bleroy/pokeymax/VHDL/SID/jsiddevice.ini

[JSIDDevice]
; hostname to listen to clients on
Hostname=127.0.0.1
; port to listen to clients on
Port=6581
; c64 clocks, almost same as us
Latency=250000

[Audio]
; Allows overriding of the default playback/record frequency. The frequency must be provided in Hertz (Hz) and by default it is set to 44100.
Frequency=48000
; Sampling method in use
Sampling=Decimate
; Size of the audio buffer (responsiveness=1024 .. stable audio=16384), must be a power of two!
Audio Buffer Size=2048

[WhatsSID]
; WhatsSID? Recognizes the currently played tune after a few seconds
Enable=false
; The server side is in fact JSIDPlay2 running in server mode
Url=https://haendel.ddns.net:8443/jsidplay2service/JSIDPlay2REST
Username=jsidplay2
Password=jsidplay2!
; Capture the last N seconds for tune recognition
Capture Time=15
; Tune recognition will be done periodically after this time (in seconds) 
Match Retry Time=15
; Minimum relative confidence to recognize a tune with confidence
Minimum Relative Confidence=4.5

[FilterLight8580]
Filter8580CurvePosition = 13400

[FilterAverage8580]
Filter8580CurvePosition = 12500

[FilterDark8580]
Filter8580CurvePosition = 11700

[FilterLightest6581]
Filter6581CurvePosition = 0.1

[FilterLighter6581]
Filter6581CurvePosition = 0.3

[FilterLight6581]
Filter6581CurvePosition = 0.4

[FilterAverage6581]
Filter6581CurvePosition = 0.5

[FilterDark6581]
Filter6581CurvePosition = 0.6

[FilterDarker6581]
Filter6581CurvePosition = 0.7

[FilterDarkest6581]
Filter6581CurvePosition = 0.9

[FilterJSidDevice10_6581]
Attenuation=0.5
Nonlinearity=3.3e6
VoiceNonlinearity=0.96
Type3BaseResistance=1.3e6
Type3Offset=1.9e7
Type3Steepness=1.0066
Type3MinimumFETResistance=1.8e4
ResonanceFactor=1.0

[FilterJSidDevice10_8580]				
Type4K=6.55
Type4B=20
VoiceNonlinearity=1.0
ResonanceFactor=1.0

[FilterTrurl8580R5_1489]
Type4K=5.7
Type4B=20
VoiceNonlinearity=1.0
ResonanceFactor=1.0

[FilterTrurl8580R5_3691]
Type4K=6.55
Type4B=20
VoiceNonlinearity=1.0
ResonanceFactor=1.0

[FilterReSID6581]
Attenuation=0.5
Nonlinearity=3.3e6
VoiceNonlinearity=0.96
Type3BaseResistance=1537690.1305811733
Type3Offset=76322577.13241087
Type3Steepness=1.0072175060266852
Type3MinimumFETResistance=19114.018733380854
ResonanceFactor=1.0

[FilterAlankila6581R4AR_3789]
Attenuation=0.5
Nonlinearity=3.3e6
VoiceNonlinearity=0.9613160610660189
Type3BaseResistance=1147036.4394268463
Type3Offset=274228796.97550374
Type3Steepness=1.0066634233403395
Type3MinimumFETResistance=16125.154840564108
ResonanceFactor=1.0

[FilterAlankila6581R3_3984_1]
Attenuation=0.5
Nonlinearity=3.3e6
VoiceNonlinearity=0.96
Type3BaseResistance=1522171.922983084
Type3Offset=21729926.667291082
Type3Steepness=1.004994802537475
Type3MinimumFETResistance=14299.149638099827
ResonanceFactor=1.0

[FilterAlankila6581R3_3984_2]
Attenuation=0.5
Nonlinearity=3.3e6
VoiceNonlinearity=0.96
Type3BaseResistance=1613349.4942964897
Type3Offset=67122945.35403329
Type3Steepness=1.005727808339829
Type3MinimumFETResistance=15462.006399118263
ResonanceFactor=1.0

[FilterLordNightmare6581R3_4285]
Attenuation=0.5
Nonlinearity=3.3e6
VoiceNonlinearity=0.96
Type3BaseResistance=1.55e6
Type3Offset=2.5e8
Type3Steepness=1.006
Type3MinimumFETResistance=1.9e4
ResonanceFactor=1.0

[FilterLordNightmare6581R3_4485]
Attenuation=0.5
Nonlinearity=3.3e6
VoiceNonlinearity=0.96
Type3BaseResistance=1399768.3253307983
Type3Offset=553018906.8926692
Type3Steepness=1.0051493199361266
Type3MinimumFETResistance=11961.908870403166
ResonanceFactor=1.0

[FilterLordNightmare6581R4_1986S]
Attenuation=0.5
Nonlinearity=3.3e6
VoiceNonlinearity=0.96
Type3BaseResistance=1250736.2235895505
Type3Offset=1521187976.8735676
Type3Steepness=1.005543646897986
Type3MinimumFETResistance=8581.78418415723
ResonanceFactor=1.0

[FilterZrX6581R3_0384]
Attenuation=0.5
Nonlinearity=3.3e6
VoiceNonlinearity=0.96
Type3BaseResistance=1.9e6
Type3Offset=8.5e7
Type3Steepness=1.0058
Type3MinimumFETResistance=2e4
ResonanceFactor=1.0

[FilterZrX6581R3_1984]
Attenuation=0.5
Nonlinearity=3.3e6
VoiceNonlinearity=0.96
Type3BaseResistance=1.83e6
Type3Offset=2.6e9
Type3Steepness=1.0064
Type3MinimumFETResistance=2.5e4
ResonanceFactor=1.0

[FilterZrx6581R3_3684]
Attenuation=0.5
Nonlinearity=3.3e6
VoiceNonlinearity=0.96
Type3BaseResistance=1.65e6
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
ResonanceFactor=1.0

[FilterEnigma6581R3_1585]
Attenuation=0.5
Nonlinearity=3.3e6
VoiceNonlinearity=0.96
Type3BaseResistance=1119380.8539989102
Type3Offset=257709531.3343812
Type3Steepness=1.0073881870085593
Type3MinimumFETResistance=20269.79137269368
ResonanceFactor=1.0
