bleroy/pokeymax/VHDL/int_osc/synthesis/int_osc.vhd

-- int_osc.vhd

-- Generated using ACDS version 20.1 720

library IEEE;
use IEEE.std_logic_1164.all;
use IEEE.numeric_std.all;

entity int_osc is
	port (
		clkout : out std_logic;        -- clkout.clk
		oscena : in  std_logic := '0'  -- oscena.oscena
	);
end entity int_osc;

architecture rtl of int_osc is
	component altera_int_osc is
		generic (
			DEVICE_FAMILY   : string := "";
			DEVICE_ID       : string := "UNKNOWN";
			CLOCK_FREQUENCY : string := "UNKNOWN"
		);
		port (
			oscena : in  std_logic := 'X'; -- oscena
			clkout : out std_logic         -- clk
		);
	end component altera_int_osc;

begin

	int_osc_0 : component altera_int_osc
		generic map (
			DEVICE_FAMILY   => "MAX 10",
			DEVICE_ID       => "08",
			CLOCK_FREQUENCY => "116"
		)
		port map (
			oscena => oscena, -- oscena.oscena
			clkout => clkout  -- clkout.clk
		);

end architecture rtl; -- of int_osc
